cris-maillo/frontleft-tutorial/display/secrets.example.h

// Copy this file to secrets.h and fill it in. secrets.h is gitignored — never commit it.

const char* WIFI_SSID = "your-wifi-name";
const char* WIFI_PASS = "your-wifi-password";
const char* EVENTS_URL = "https://raw.githubusercontent.com/<your-github-user>/<your-repo>/main/events.json";

// Only needed if your repo is private: a fine-grained token with Contents: read-only.
// Leave empty ("") for a public repo.
const char* GH_TOKEN = "";
